Kelvysb/HotKeyPad/Arduino/Circuit_v2/HotKeypad/HotKeypad.kicad_sch

## KiCad design Arduino/Circuit_v2/HotKeypad/HotKeypad.kicad_sch (2025-01-16)

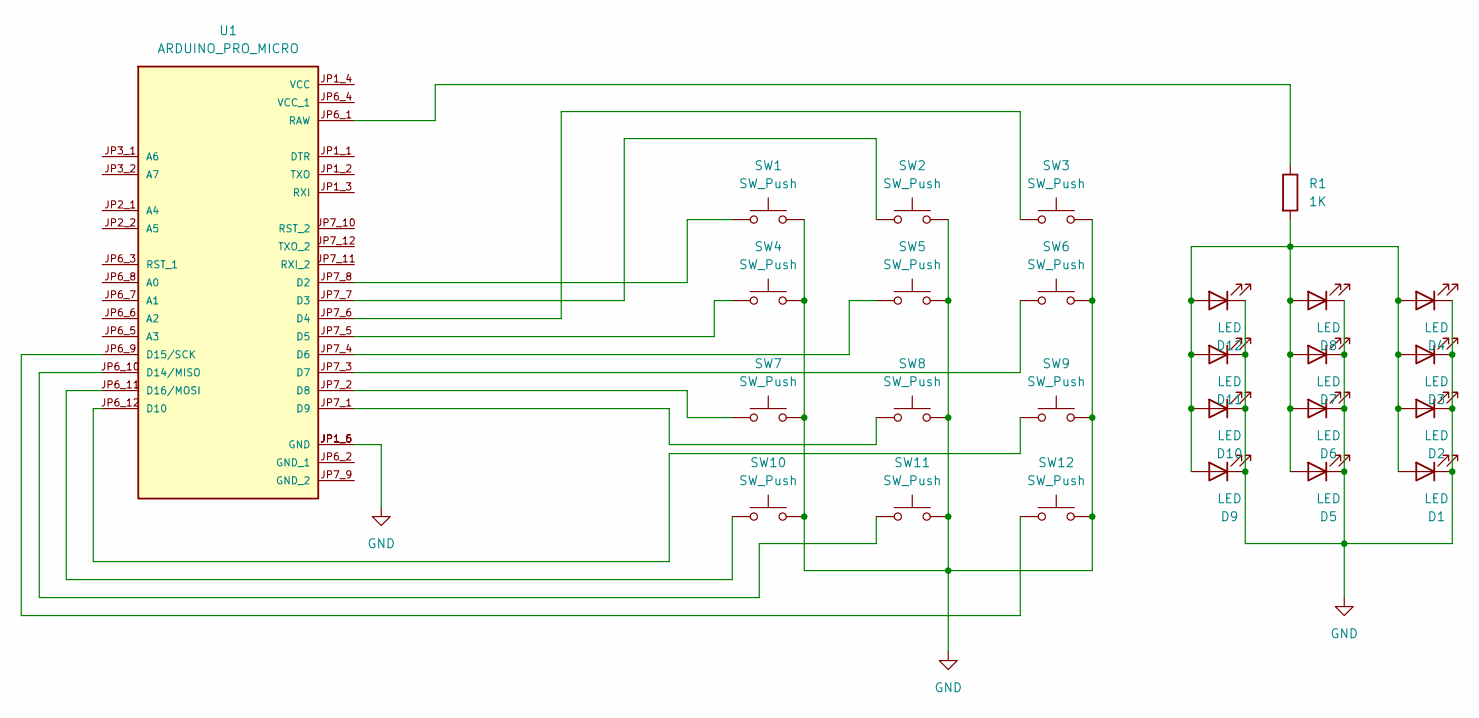
[picture p22: schematic HotKeypad.kicad_sch]

Parts:
D1, D2, D3, D4, D5, D6, D7, D8, D9, D10, D11, D12: LED
R1: 1K
SW1, SW2, SW3, SW4, SW5, SW6, SW7, SW8, SW9, SW10, SW11, SW12: SW_Push
U1: ARDUINO_PRO_MICRO; MODULE_ARDUINO_PRO_MINI; PARTREV N/A

Connections:
GND: D1.1 (K), D2.1 (K), D3.1 (K), D4.1 (K), D5.1 (K), D6.1 (K), D7.1 (K), D8.1 (K), D9.1 (K), D10.1 (K), D11.1 (K), D12.1 (K), SW1.2, SW2.2, SW3.2, SW4.2, SW5.2, SW6.2, SW7.2, SW8.2, SW9.2, SW10.2, SW11.2, SW12.2, U1.JP1_5 (GND), U1.JP1_6 (GND)
unnamed: D1.2 (A), D2.2 (A), D3.2 (A), D4.2 (A), D5.2 (A), D6.2 (A), D7.2 (A), D8.2 (A), D9.2 (A), D10.2 (A), D11.2 (A), D12.2 (A), R1.2
unnamed: R1.1, U1.JP6_1 (RAW)
unnamed: SW1.1, U1.JP7_8 (D2)
unnamed: SW2.1, U1.JP7_7 (D3)
unnamed: SW3.1, U1.JP7_6 (D4)
unnamed: SW4.1, U1.JP7_5 (D5)
unnamed: SW5.1, U1.JP7_4 (D6)
unnamed: SW6.1, U1.JP7_3 (D7)
unnamed: SW7.1, U1.JP7_2 (D8)
unnamed: SW8.1, U1.JP7_1 (D9)
unnamed: SW9.1, U1.JP6_12 (D10)
unnamed: SW10.1, U1.JP6_11 (D16/MOSI)
unnamed: SW11.1, U1.JP6_10 (D14/MISO)
unnamed: SW12.1, U1.JP6_9 (D15/SCK)
